jpconstantineau/CNC_encoder_pad/images/leds.jpg

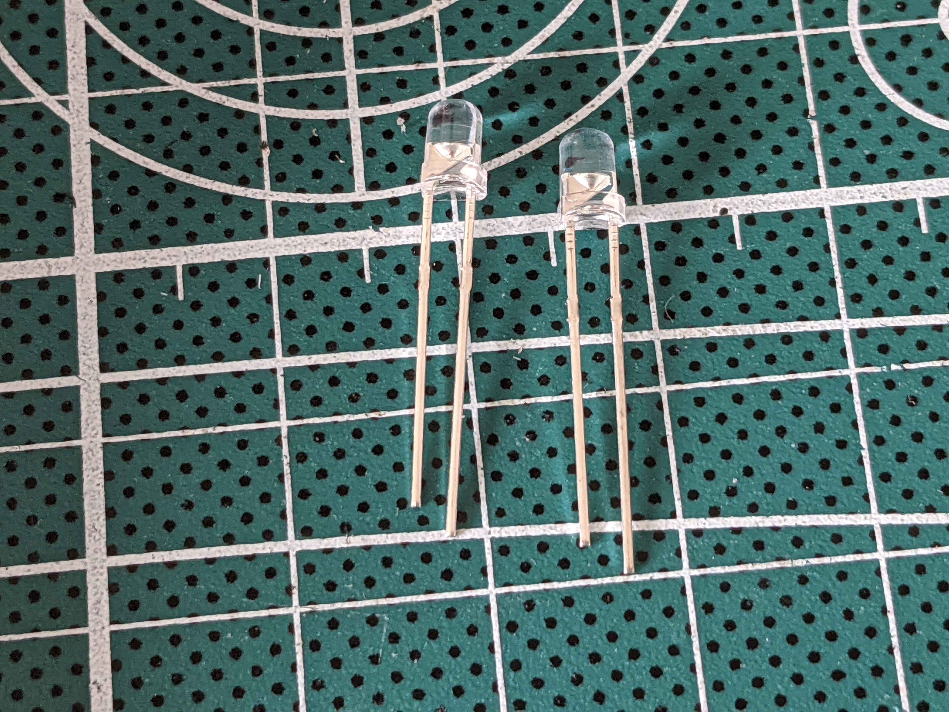
images/leds.jpg
