jpconstantineau/CNC_encoder_pad/images/resistor_position.jpg

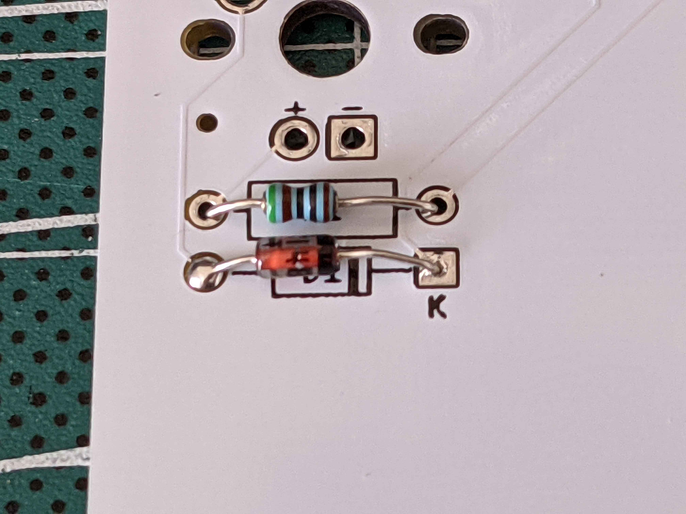
images/resistor_position.jpg
